kinoshita-lab/moids2.x.x/moidsApp/moids_arduino/Moids.cpp

#include "Arduino.h"
#include "Moids.h"
#include <digitalWriteFast.h>
#include "workaround.h"
#include "debug.h"
#include "common.h"
// 反応するときにデカすぎる場合をハネる。値が大きい方が反応しやすい。最小は0。
const int Moids::MOIDS_INPUT_TOO_BIG = 100;

// 状態が変わった時にちょっと待つ（誤動作防止用) 最小は0。最大でも10くらい。
const int Moids::DELAY_FOR_STATE_TRANSITION = 0;

// 音が入ってきたかどうか？のチェックをちょっと厳密にする。
const bool Moids::STRICT_CHECKING = false;

// ここから下は基本データ
const int Moids::sound_table_length = 5;
/**
 *  relay on time.
 *  number of cycles of 125usec timer tick
 */
const int Moids::sound_table_on[] =
    {
        125 / 125,
        125 / 125,
        250 / 125,
        125 / 125,
        375 / 125,
};

/**
 * relay off time.
 * number of cycles of 125usec timer tick
 */
const int Moids::sound_table_off[] =
    {
        125 / 125,
        250 / 125,
        250 / 125,
        500 / 125,
        375 / 125,
};

/**
 * sound drations.
 * number of cycles of 125usec timer tick
 */
const int Moids::sound_durations[] =
    {
        150,
        150,
        150,
        150,
        150,
};

int Moids::id_count = 0;
Moids::Moids()
{
    m_id = id_count;
    id_count++;
}

void Moids::init()
{
    m_dontReadCounter               = 0;
    m_numOtherMoids                 = 0;
    m_firstTimeAfterStateTransition = false;
    m_relayOnTimeCounter            = 0;
    m_waitAfterDetectCounter        = 0;
    m_timerCounter                  = 0;
    m_micOffset                     = 0;
    m_nopWait                       = (unsigned long)500;
    m_nopWaitCounter                = 0;
    m_needOscillation               = false;
    m_relayOffTime                  = 0;
    m_relayOffCounter               = 0;
    m_oscillatorCountMax            = 0;
    m_oscillation_high              = false;

    for (int i = 0; i < NUM_OTHER_MOIDS; i++) {
        m_otherMoids[i] = NULL;
    }

    makeOffset();
    changeState(ReadAnalog);
}

void Moids::makeOffset()
{
    float offset = 0.f;

    for (int i = 0; i < 100; i++) {
        offset += 0.01 * analogRead(m_inputMicPin);
    }

    m_micOffset = (int)offset;
    DEBUG_PRINTLN("Mic offset: " + String(m_micOffset));
}

void Moids::setMicThreshold(const int thres)
{
    m_micThreshold = thres;
}

void Moids::setRelayOnTime(const int time)
{
    m_relayOnTime = time;
}

void Moids::setWaitAfterSoundDetect(const int time)
{
    m_waitAfterDetect = time;
}

void Moids::loop()
{
    if (ReadAnalog == m_state) {
        readAnalogInput();
    }

    if (m_tick_need_processed) {
        m_tick_need_processed = false;
        (this->*m_timerFunction)();
    }
}

void Moids::readAnalogInput()
{
    if (m_dontReadCounter) {
        return;
    }

    if (m_firstTimeAfterStateTransition) {
        m_firstTimeAfterStateTransition = false;
        makeOffset();

        int read = analogRead(m_inputMicPin) - m_micOffset;
        for (int i = 0; i < MIC_INPUT_ARRAY_LENGTH; i++) {
            m_micInput[i] = read;
        }
    }

    // read Input
    m_micInput[0] = analogRead(m_inputMicPin) - m_micOffset;
    m_micInput[1] = analogRead(m_inputMicPin) - m_micOffset;

    // check threshold
    bool changed = checkInput();

    if (changed) {
        DEBUG_PRINTLN(String(m_id) + " : Mic input detected: ");
        changeState(SoundInput);
    }
}

bool Moids::checkInput()
{
    const int diff = abs(m_micInput[0] - m_micInput[1]);

    return diff > m_micThreshold;
}

// tick from MsTimer2, assuming tick cycle is 125 usec
void Moids::tick()
{
    m_timerCounter++;
    m_tick_need_processed = true;
}

void Moids::tickNopState()
{
    m_nopWaitCounter++;

    if (m_nopWait > m_nopWaitCounter) {
        return;
    }

    m_firstTimeAfterStateTransition = true;
    m_nopWaitCounter                = 0;
    analogWrite(m_outputLEDPin, LED_BRIGHTNESS_WAITING);
    changeState(ReadAnalog);
}

void Moids::tickReadAnalogState()
{
    // nop
}

void Moids::tickSoundInputState()
{
    m_waitAfterDetectCounter++;

    if (m_waitAfterDetect > m_waitAfterDetectCounter) {
        return;
    }

    m_waitAfterDetectCounter = 0;

    digitalWriteFast(m_outputRelayPin, HIGH);
    analogWrite(m_outputLEDPin, LED_BRIGHTNESS_SOUND_GENERATING);
    changeState(GenerateSound);
}

void Moids::tickGenerateSoundState()
{
    if (m_needOscillation) {
        oscillate();
        return;
    }

    m_relayOnTimeCounter++;

    if (m_relayOnTime > m_relayOnTimeCounter) {
        return;
    }

    toNop();
}

void Moids::oscillate()
{
    m_timerCounter++;

    if (m_oscillation_high) {
        if (m_timerCounter > m_relayOnTime) {
            m_timerCounter = 0;
            digitalWriteFast(m_outputRelayPin, LOW);
            m_oscillation_high = false;
        }

        return;
    }

    if (m_timerCounter > m_relayOffTime) {
        m_oscillationCount++;

        if (m_oscillationCount > m_oscillatorCountMax) {
            m_timerCounter = 0;
            toNop();
            return;
        }

        m_timerCounter = 0;
        digitalWriteFast(m_outputRelayPin, HIGH);
        m_oscillation_high = true;
    }
}

void Moids::toNop()
{
    digitalWriteFast(m_outputRelayPin, LOW);
    m_relayOnTimeCounter = 0;
    analogWrite(m_outputLEDPin, 0);
    changeState(Nop);
}

void Moids::changeState(const int state)
{
    noInterrupts();
    m_state = state;

    switch (m_state) {
    case ReadAnalog:
        m_detect1stTime                 = false;
        m_firstTimeAfterStateTransition = true;
        m_timerFunction                 = &Moids::tickReadAnalogState;
        analogWrite(m_outputLEDPin, LED_BRIGHTNESS_WAITING);
        break;
    case SoundInput:
        broadCastGenerateSoundState(true);
        determineSound();
        m_timerFunction = &Moids::tickSoundInputState;
        analogWrite(m_outputLEDPin, LED_BRIGHTNESS_INPUT_DETECTED);
        break;
    case GenerateSound:
        m_timerFunction = &Moids::tickGenerateSoundState;
        break;
    case Nop:
        broadCastGenerateSoundState(false);
        m_timerFunction = &Moids::tickNopState;
        break;
    default:
        break;
    }
    interrupts();

    if (DELAY_FOR_STATE_TRANSITION) {
        delay_comp(DELAY_FOR_STATE_TRANSITION);
    }
}

void Moids::setInputMicPin(const int pin)
{
    m_inputMicPin = pin;
    pinMode(pin, INPUT);
}

void Moids::setOutputLEDPin(const int pin)
{
    m_outputLEDPin = pin;
    pinMode(pin, OUTPUT);
}

void Moids::setOutputRelayPin(const int pin)
{
    m_outputRelayPin = pin;
    pinMode(pin, OUTPUT);
}

void Moids::registerOtherMoids(Moids* moids)
{
    m_otherMoids[m_numOtherMoids] = moids;
    m_numOtherMoids++;
}

void Moids::broadCastGenerateSoundState(bool start)
{
    for (int i = 0; i < m_numOtherMoids; i++) {
        m_otherMoids[i]->receiveOtherMoidsMessageSoundState(start, m_outputRelayPin);
    }
}

void Moids::receiveOtherMoidsMessageSoundState(bool start, int relayPin)
{
    if (start) {
        //DEBUG_PRINTLN(String(m_id) + " : Received sound start from relay pin " + String(relayPin));
        m_dontReadCounter++;
    } else {
        //DEBUG_PRINTLN(String(m_id) + " : Received sound stop from relay pin " + String(relayPin));
        m_dontReadCounter--;
    }
}

void Moids::determineSound()
{
    m_timerCounter = 0;

    // randomize sound
    const int soundIndex = random(sound_table_length + 1);
    
    m_relayOnTime  = sound_table_on[soundIndex];
    m_relayOffTime = sound_table_off[soundIndex];

    m_needOscillation = true;//(soundIndex < 0);

	m_relayOnTime = sound_table_on[soundIndex];
	m_relayOffTime = sound_table_off[soundIndex];


	if (m_needOscillation)
	{
        DEBUG_PRINTLN(String(m_id) + " : Generating sound with oscillation, index: " + String(soundIndex));
		m_timerCounter = 0;
		m_oscillation_high = true;
		digitalWriteFast(m_outputRelayPin, HIGH);
		m_oscillatorCountMax =  sound_durations[soundIndex];
		m_oscillationCount = 0;
	}
}
